OpenGUT/OpenGUT/Firmware/Firmware_Button_based_selection/src/SD.h

#ifndef SD_H
#define SD_H

#include <stddef.h>

#define SD_INIT_ERR_DISK_ACCESS   (-1001)
#define SD_INIT_ERR_MOUNT         (-1002)
#define SD_INIT_ERR_STATVFS       (-1003)

int SD_Init(void);
int SD_Write_Hello_File_With_Led_Status(void);
int SD_Write_Hello_File(void);
int SD_Read_File(const char *path, char *buffer, size_t buffer_size);

#endif /* SD_H */
